ViralEntity/HexEnder/STLs/HextrudORT Mods/HexE6_3010_Shroud_v1.stl

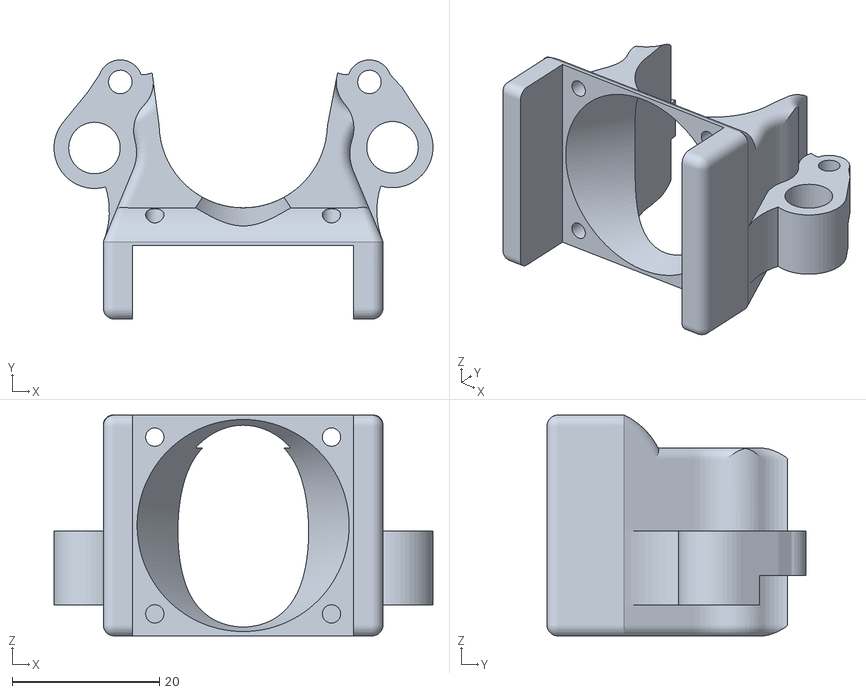
[picture p18: CAD file, 2021-08-04]
STLs/HextrudORT Mods/HexE6_3010_Shroud_v1.stl
51.5 x 35.2 x 30.0
